paradissimon/GuitarAmplifier/Spice/Guitar Amplifier.asc

C0: cap; 47µF
C1: cap; 47µF
C2: cap; 47µF
C3: cap; 47µF
C4: cap; 10µF
C10: cap; 1.0µF
C11: cap; 0.0022µF
C20: cap; 100µF
D1: diode; UF4007
D2: diode; UF4007
D3: diode; UF4007
D4: diode; UF4007
L1: ind2; 5H
L2: ind2; 5H
Q1: npn2; 2N5551
R1: res; 20k
R2: res; 1K
R3: res; 10K
R4: res; 1000
R5: res; 820k
R6: res; 200k
R7: res; 27k
R10: res; 1000k
R11: res; 33k
R12: res; 1K
R13: res; 10k
R20: res; 5.6K
R21: res; 1500
R22: res; 150
Rload: res; 6000
U1: KSC5305F
V1: voltage; SINE(0 283 60 0 0 0); Rser=10
V1A: triode; NH12AX7
V1B: triode; NH12AX7
V2: tetrode; 6BQ5
V3: voltage; SINE(0 283 60 0 0 180); Rser=10
Vinput: voltage; 0V; AC 0.01
VR1_A: res; 100k
VR1_B: res; 470k
Named nets: B3, Vin, B1, B2, 0, V1, V2, stage1, V2A, V2K, V1K, V2G, Vout, V2S, B0, Q1E, HElev
500K LOG POT
.tran 15s startup uic
.inc dmtriodep.inc
.inc 6bq5.inc
.inc KSC5305F.lib
.model 1N4007 D(Rs=0.010 Tt=2u Cjo=15p Vj=0.6 BV=1000 Ibv=5u)
.model UF4007 D(Rs=0.161 Tt=75n Cjo=17p Vj=0.6 BV=1000 Ibv=10u)
.model 2N5551 NPN (Is=2.511f Xti=3 Eg=1.11 Vaf=100 Bf=242.6 Ne=1.249 Ise=2.511f Ikf=.3458 Xtb=1.5 Br=3.197 Nc=2 Isc=0 Ikr=0 Rc=1 Cjc=4.883p Mjc=.3047 Vjc=.75 Fc=.5 Cje=18.79p Mje=.3416 Vje=.75 Tr=1.202n Tf=560p Itf=50m Vtf=5 Xtf=8 Rb=10)
K1 L1 L2 1
3W
1.6V
In actual amp with 124 VAC mains, B0 is 275 VDC
V1/V3 adjusted until simulated B0 matches.
The simulation results are very close to actual measurements.
The heater DC elevation, HElev, is fed to a humdinger pot
Power transformer is
Hammond 269EX
Output transformer is Doberman 20W SE with a 6000 ohms primary.
An ideal transformer connected to a 6000 ohms resistive load
is used to simplify simulation.
The input grid resistor, R13, was ommitted in
the actual build with no unwanted effects.
U1 is a high voltage power NPN BJT transistor
Q1 is a small signal NPN BJT transistor
 
U1 in build is Fairchild FJPF5027OTU (TO-220F plastic package with heat sink)
Q1 in build is Fairchild 2N5551BU (TO-92 package)
 
Simulation uses another power BJT since that's the only power BJT spice model I found.
3W
